NorthernWidget/Instrumentation-Amp/CMP3_Amp.asc

C1: cap; 0.1µF
C2: cap; 0.1µF
R1: res; 1k
R2: res; 62k
R3: res; {R1}
R4: res; {R0}
R5: res; {R0}
R6: res; {R0}
R7: res; 1k
U1: LTC2054
U2: LTC2054
V1: voltage; 12e-6
V2: voltage; 3.3
V3: voltage; {Voff1}
V4: voltage; {Voff2}
Named nets: 0, 3v3, Vgain, B, A
.param R0 1Meg
.param R1 590k
.tran 1e-3
.step param Voff1 0 5e-6 1e-6
.step param Voff2 0 5e-6 1e-6
