NorthernWidget/Instrumentation-Amp/CMP3_Amp_AC.asc

C1: cap; 0.1µF
C2: cap; 0.1µF
R1: res; 1k
R2: res; 62k
R3: res; {R1}
R4: res; {R0}
R5: res; {R0}
R6: res; {R0}
R7: res; 1k
U1: LTC2054
U2: LTC2054
V1: voltage; SINE(0 1m {Freq})
V2: voltage; 3.3
Named nets: 0, 3v3, Vgain, B, A
.param t0=10
.tran 0 {t0+25/freq} {t0}
.step dec param freq 0.1 500 5
.save V(a) V(b)
.option plotwinsize=0 numdgt=15
.param R0 1Meg
.param R1 590k
.measure Aavg avg V(a)
.measure Bavg avg V(b)
.measure Are avg (V(a)-Aavg)*cos(360*time*Freq)
.measure Aim avg -(V(a)-Aavg)*sin(360*time*Freq)
.measure Bre avg (V(b)-Bavg)*cos(360*time*Freq)
.measure Bim avg -(V(b)-Bavg)*sin(360*time*Freq)
.measure GainMag param 20*log10(hypot(Are,Aim) / hypot(Bre,Bim))
.measure GainPhi param mod(atan2(Aim, Are) - atan2(Bim, Bre)+180,360)-180
